tennessee-garage/dance-floor/models/Power Distribution.png

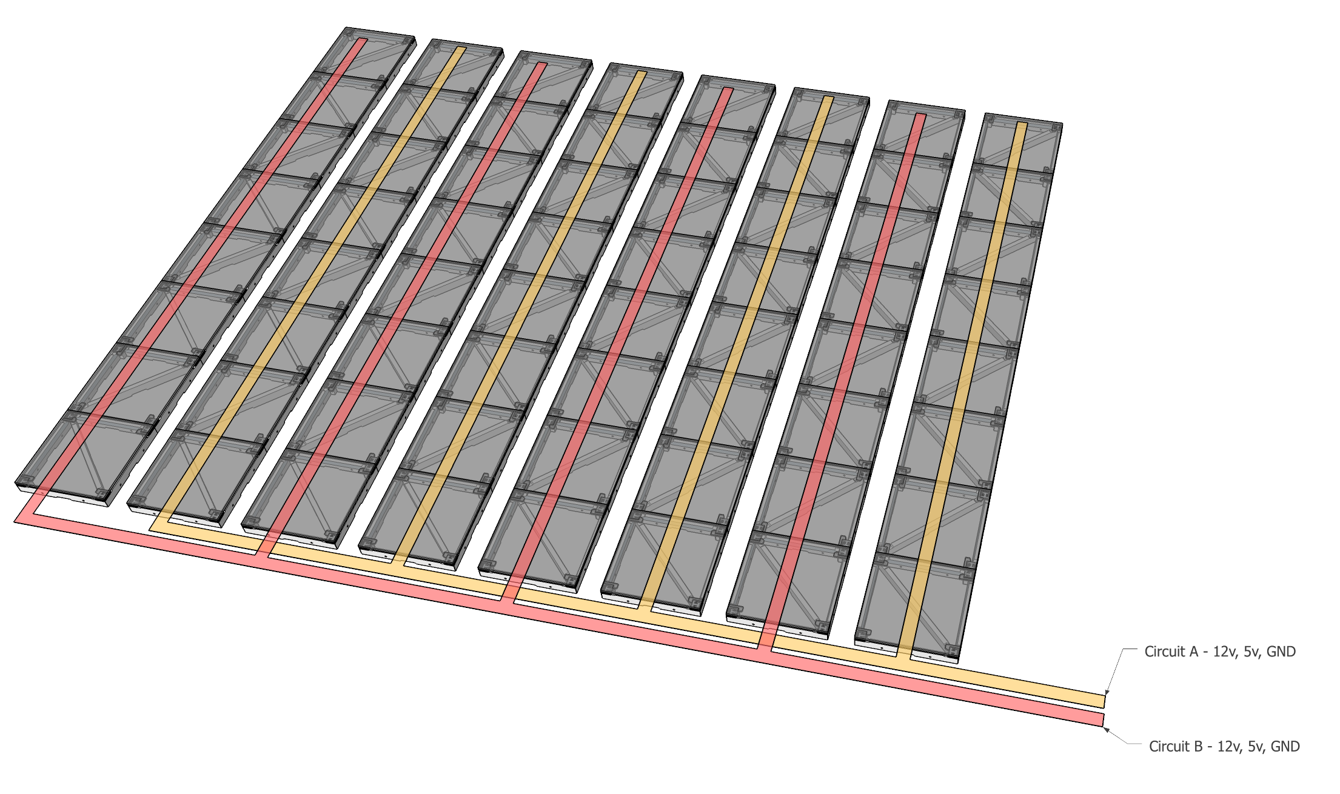
models/Power Distribution.png
