tennessee-garage/dance-floor/models/Floor Assembly - Detail.png

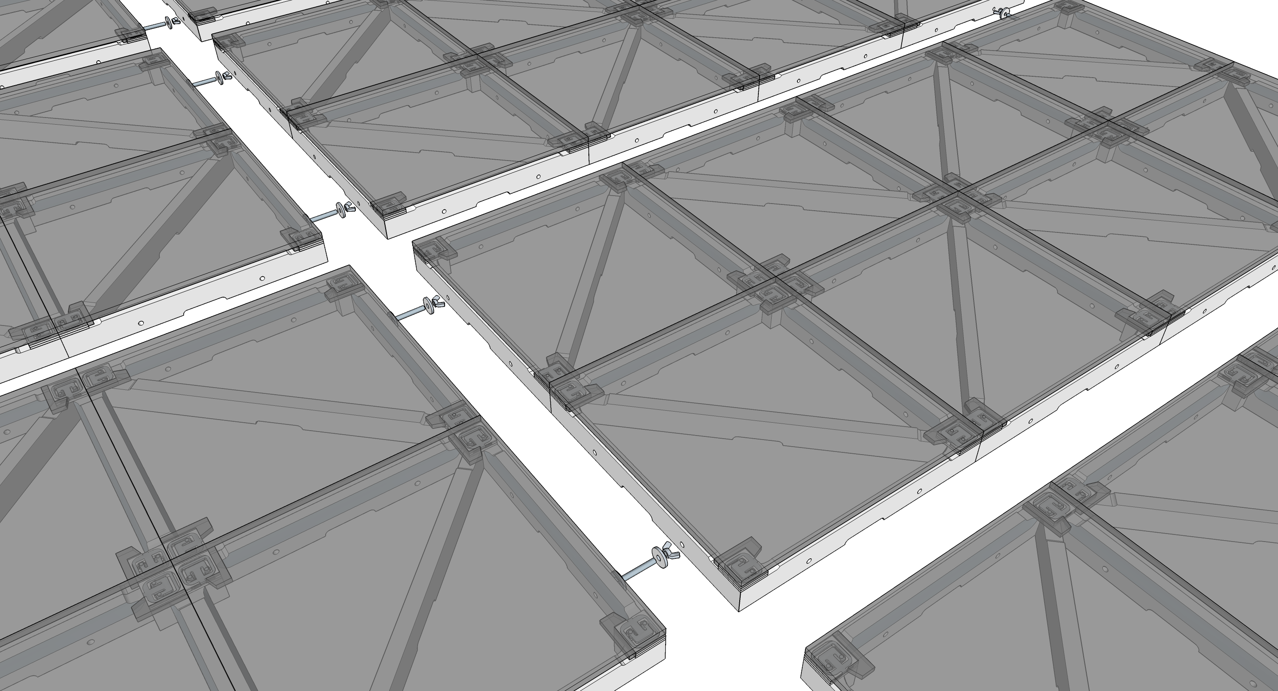
models/Floor Assembly - Detail.png
