tennessee-garage/dance-floor/models/Floor Assembly - Hardware.png

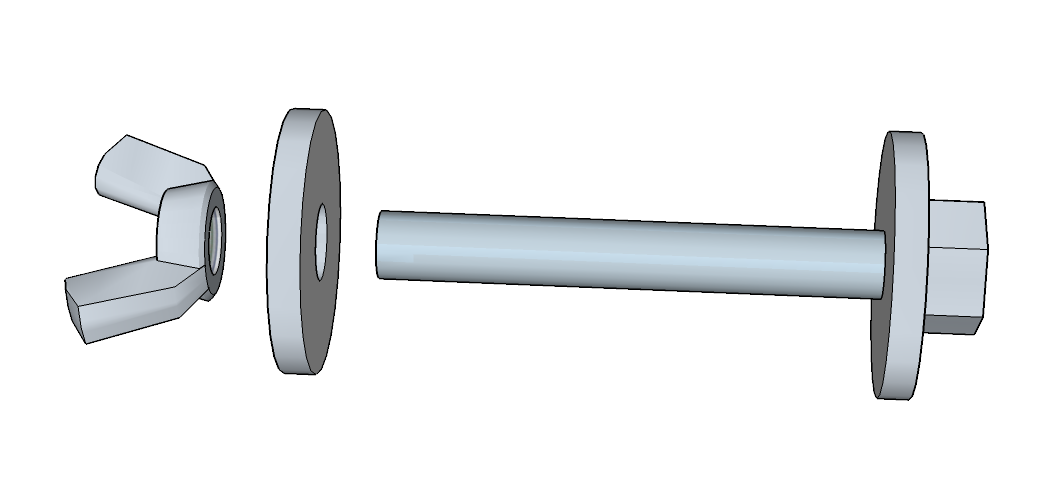
models/Floor Assembly - Hardware.png
