tennessee-garage/dance-floor/models/Floor Assembly - Overview.png

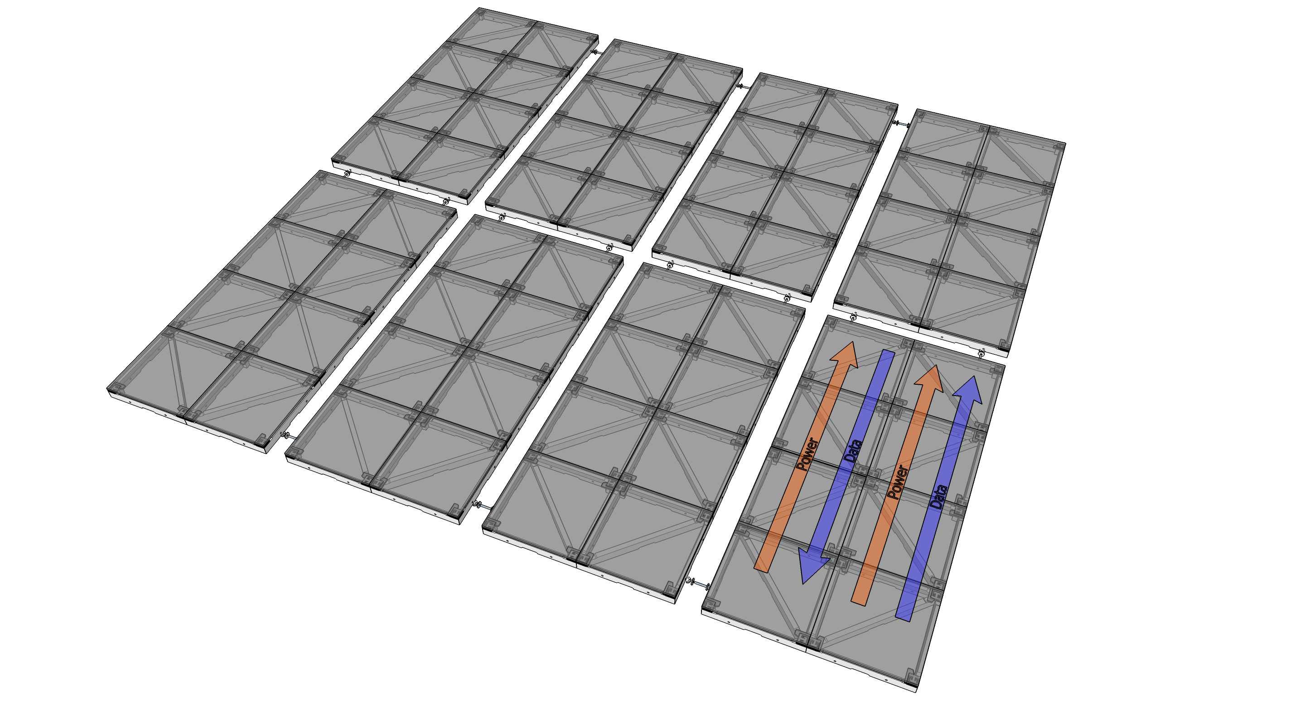
models/Floor Assembly - Overview.png
