tennessee-garage/dance-floor/floor/floor/processor/electricity.py

import logging
import math
import random

from floor.processor.base import Base
from floor.processor.utils import clocked

logger = logging.getLogger("electricity")


def dist(x1, y1, x2, y2):
    return math.sqrt((x1 - x2) ** 2 + (y1 - y2) ** 2)


class Electricity(Base):
    DECAY_RATE = 0.8
    DECAY_THRESHOLD = 0.001

    def __init__(self, **kwargs):
        super().__init__(**kwargs)

        self.arcs = {}

        # self.arc = Arc(1, 63)

        self.pixels = [[0, 0, 0] for _ in range(64)]

    @clocked(frames_per_second=24)
    def get_next_frame(self, context):
        weights = context.weights
        self.fade_frame()

        last_val = None
        new_arcs = {}
        for idx, w in enumerate(weights):
            if w > 0:
                if last_val is not None:
                    pair = f"{last_val}-{idx}"
                    logger.info(f"Pair: {pair}")
                    if pair in self.arcs:
                        new_arcs[pair] = self.arcs[pair]
                    else:
                        new_arcs[pair] = Arc(last_val, idx)

                last_val = idx

        self.arcs = new_arcs

        for arc in list(self.arcs.values()):
            self.apply_arc(arc)

        return self.pixels

    def apply_arc(self, arc):
        arc.advance()

        for idx, val in enumerate(arc.frame):
            if len(val) > 0:
                self.pixels[idx] = (
                    val  # [val * COLOR_MAXIMUM, val * COLOR_MAXIMUM, val * COLOR_MAXIMUM]
                )

    def fade_frame(self):
        for idx in range(64):
            if self.pixels[idx][0] > self.DECAY_THRESHOLD:
                self.pixels[idx][0] *= self.DECAY_RATE
                self.pixels[idx][1] *= self.DECAY_RATE
                self.pixels[idx][2] *= self.DECAY_RATE
            else:
                self.pixels[idx] = [0, 0, 0]


class Arc:
    LEAD_PATH = 1.0
    LEAD_ALTERNATE = 0.4

    def __init__(self, point1, point2):
        # Two points on the floor to arc between
        self.point1 = point1
        self.point2 = point2

        # The points translated to x & y
        self.p1x = point1 % 8
        self.p1y = int(point1 / 8)
        self.p2x = point2 % 8
        self.p2y = int(point2 / 8)

        logger.info(
            f"p1:{point1}, p2:{point2} == x1:{self.p1x}, y1:{self.p1y}, x2:{self.p2x}, y2:{self.p2y}"
        )

        # The position of the leading edge of the arc
        self.lead_x = self.p1x
        self.lead_y = self.p1y

        # The distance between the start and end point
        self.cur_distance = 0

        # Whether the arc has connected
        self.connected = False

        # Hold the arc pattern
        self.frame = [[0, 0, 0] for _ in range(64)]

    def advance(self):
        options = []
        self.set_cur_distance()

        # Upper left
        self.add_if_valid(options, self.lead_x - 1, self.lead_y - 1)

        # Upper center
        self.add_if_valid(options, self.lead_x, self.lead_y - 1)

        # Upper right
        self.add_if_valid(options, self.lead_x + 1, self.lead_y - 1)

        # Middle right
        self.add_if_valid(options, self.lead_x + 1, self.lead_y)

        # Lower right
        self.add_if_valid(options, self.lead_x + 1, self.lead_y + 1)

        # Lower middle
        self.add_if_valid(options, self.lead_x, self.lead_y + 1)

        # Lower left
        self.add_if_valid(options, self.lead_x - 1, self.lead_y + 1)

        # Middle left
        self.add_if_valid(options, self.lead_x - 1, self.lead_y)

        if len(options) == 0:
            return

        pick = random.randint(0, len(options) - 1)
        for idx, point in enumerate(options):
            if idx == pick:
                self.frame[point[0] + point[1] * 8] = [0, 0, 1000]
                self.lead_x = point[0]
                self.lead_y = point[1]
            else:
                self.frame[point[0] + point[1] * 8] = [500, 0, 0]

        if self.connected:
            # Start over again
            self.lead_x = self.p1x
            self.lead_y = self.p1y
            self.clear_frame()
            self.connected = False

    def set_cur_distance(self):
        self.cur_distance = self.dist_to_p2(self.lead_x, self.lead_y)

    def add_if_valid(self, options, x, y):
        d = self.dist_to_p2(x, y)
        if d != -1 and d < self.cur_distance:
            options.append((x, y))
        if d == 0:
            self.connected = True

    def dist_to_p2(self, x, y):
        if x < 0 or x > 7 or y < 0 or y > 7:
            return -1

        return dist(x, y, self.p2x, self.p2y)

    def clear_frame(self):
        self.frame = [[0, 0, 0] for _ in range(64)]
