tennessee-garage/dance-floor/floor/floor/processor/land_mines.py

import math
import random

import floor.util.color_utils as color_utils
from floor.processor.base import Base
from floor.processor.constants import COLOR_MAXIMUM
from floor.processor.utils import clocked

life_time = 4


class LandMines(Base):
    def __init__(self, **kwargs):
        super().__init__(**kwargs)
        self.pixels = []
        self.mines = []
        self.walkers = self.init_walkers()
        self.palette = color_utils.get_random_palette()
        self.palette_length = len(self.palette)
        for x in range(0, 8):
            for y in range(0, 8):
                self.pixels.append((0, 0, 0))

    @staticmethod
    def init_walkers():
        walkers = list()
        walkers.append({"x": 0, "y": 0})
        walkers.append({"x": 0, "y": 7})
        walkers.append({"x": 7, "y": 0})
        walkers.append({"x": 7, "y": 7})
        return walkers

    def get_walker(self):
        walker = self.walkers[random.randint(0, 2)]
        # take a random step
        walker["x"] += random.randint(-1, 1)
        if walker["x"] < 0:
            walker["x"] = 0
        if walker["x"] > 7:
            walker["x"] = 7
        walker["y"] += random.randint(-1, 1)
        if walker["y"] < 0:
            walker["y"] = 0
        if walker["y"] > 7:
            walker["y"] = 7
        return walker

    def build_mine(self, x, y):
        t = life_time

        idx = random.randint(0, self.palette_length - 1)
        return {"x": x, "y": y, "t": t, "color": self.palette[idx]}

    # For each mine in mines:
    # 1. If delta_time < life_time/2 Increment by: velocity * delta_time / radius
    # 2. If delta_time > life_time/2 Decrement by: velocity * delta_time / radius
    # 3. If delta_time > life_time, remove mine
    @clocked(frames_per_second=24)
    def get_next_frame(self, context):
        chance = random.random()
        if chance > 0.95:
            walker = self.get_walker()
            x = walker["x"]
            y = walker["y"]
            mine = self.build_mine(x, y)
            self.mines.append(mine)
            self.pixels[mine["y"] * 8 + mine["x"]] = mine["color"]

        time_delta = 0.1
        velocity = 0.0003 * COLOR_MAXIMUM
        live_mines = []
        for index in range(len(self.mines)):
            mine = self.mines[index]
            mine["t"] -= time_delta
            delta_time = life_time - mine["t"]
            color = mine["color"]
            toggle = 1

            # when the mine hits half a life_time, reverse the explosion
            if mine["t"] < life_time / 2:
                toggle = -1

            # if the mine has time left, compute explosion, store it in live_mines for next time
            if mine["t"] > 0.0:
                live_mines.append(mine)
                for y in range(0, 8):
                    for x in range(0, 8):
                        next_pixel = self.pixels[y * 8 + x]
                        radius = math.sqrt(
                            (x - mine["x"]) * (x - mine["x"]) + (y - mine["y"]) * (y - mine["y"])
                        )

                        # don't divide by zero :)
                        if radius > 0:
                            delta = toggle * velocity * delta_time / radius
                            next_red = next_pixel[0] + delta * color[0]
                            next_blue = next_pixel[1] + delta * color[1]
                            next_green = next_pixel[2] + delta * color[2]
                            # don't let values go negative
                            if next_blue < 0:
                                next_blue = 0
                            if next_red < 0:
                                next_red = 0
                            if next_green < 0:
                                next_green = 0
                            self.pixels[y * 8 + x] = (next_red, next_blue, next_green)

            # if the mine doesn't have time left, 0 it out and don't add it to live_mines
            else:
                self.pixels[mine["y"] * 8 + mine["x"]] = (0, 0, 0)

        self.mines = live_mines

        return self.pixels
