tennessee-garage/dance-floor/floor/floor/processor/animator.py

import importlib

from floor.processor.base import Base
from floor.processor.constants import COLOR_MAXIMUM
from floor.processor.utils import clocked
from floor.util.color_utils import scale_color


class Animator(Base):
    DEFAULT_ANIMATION = "gods_eye"

    def __init__(self, **kwargs):
        super().__init__(**kwargs)

        animation = kwargs.get("animation", self.DEFAULT_ANIMATION)

        module = importlib.import_module(f"floor.processor.animations.{animation}")
        self.animation = module.anim()
        self.floor_frame = 0
        self.animation_frame = 0
        self.fps_reduction = 2

    @clocked(frames_per_second=24)
    def get_next_frame(self, context):
        pixels = self.animation[self.animation_frame]

        if self.floor_frame % self.fps_reduction == 0:
            self.animation_frame = (self.animation_frame + 1) % len(self.animation)

        self.floor_frame = (self.floor_frame + 1) % 24

        pixels = [scale_color(p, COLOR_MAXIMUM / 255.0) for p in pixels]
        return pixels
