tennessee-garage/dance-floor/floor/floor/processor/ripple_pulse.py

import math

from floor.processor.ripple import Ripple
from floor.processor.utils import clocked


class RipplePulse(Ripple):
    # 0.75 is good for long pulses
    DECAY = 4
    OMEGA = 2 * math.pi

    # How much distance translates the time value sent to the decay method.
    # A number between 0.02 and 0.18 seems to look best.
    #  - Lower than 0.02 and the whole floor seems to flash at once
    #  - higher than 0.18 and there are too many striations and it looks noisy, not smooth
    DISTANCE_FACTOR = 0.03

    def __init__(self, **kwargs):
        super().__init__(**kwargs)

    @clocked(frames_per_beat=0.5)
    def reset_on_beat(self, context):
        self.t_start = context.clock
        self.hue += self.hue_rotation
        if self.hue > 1.0:
            self.hue -= 1.0
