tennessee-garage/dance-floor/floor/floor/processor/spiral_beat.py

from floor.processor.spiral import Spiral
from floor.processor.utils import clocked


class SpiralBeat(Spiral):
    @clocked(frames_per_beat=1)
    def get_next_frame(self, weights):
        super().get_next_frame(weights)
