tennessee-garage/dance-floor/poc_test/i2cCommands.h

//
// Created by Garth Webb on 3/18/17.
//

#ifndef DEMO2_I2CCOMMANDS_H
#define DEMO2_I2CCOMMANDS_H

void init_i2c(void);
void handle_i2c_command_last(void);
void handle_i2c_command_request_weight(void);
void handle_i2c_command_set_led(void);
void handle_i2c_command(void);
void handle_i2c(void);

#endif //DEMO2_I2CCOMMANDS_H
