tennessee-garage/dance-floor/floor/floor/processor/test.py

from floor.processor.base import Base
from floor.processor.constants import COLOR_MAXIMUM
from floor.processor.utils import clocked


class Test(Base):
    SLOW_CYCLE = 30
    FAST_CYCLE = 2

    def __init__(self, **kwargs):
        super().__init__(**kwargs)

        # helpful colors
        dark = (0, 0, 0)
        red = (COLOR_MAXIMUM, 0, 0)
        blue = (0, COLOR_MAXIMUM, 0)
        green = (0, 0, COLOR_MAXIMUM)

        # define cycles
        self.cycles = []
        # full-floor cycles
        self.cycles.append({"floor": self.init_floor(red), "duration": self.SLOW_CYCLE})
        self.cycles.append({"floor": self.init_floor(blue), "duration": self.SLOW_CYCLE})
        self.cycles.append({"floor": self.init_floor(green), "duration": self.SLOW_CYCLE})

        # cycles for individual squares
        for c in ["red", "blue", "green"]:
            for i in range(0, (self.FLOOR_WIDTH * self.FLOOR_HEIGHT)):
                floor = self.init_floor(dark)
                floor[i] = eval(c)
                self.cycles.append({"floor": floor, "duration": self.FAST_CYCLE})

        self.current_cycle = 0
        self.countdown = self.cycles[0]["duration"]

    def init_floor(self, initial_value):
        frame = []
        for x in range(0, (self.FLOOR_WIDTH * self.FLOOR_HEIGHT)):
            frame.append(initial_value)
        return frame

    @clocked(frames_per_second=24)
    def get_next_frame(self, context):
        self.countdown -= 1
        if self.countdown == 0:
            self.current_cycle += 1
            if self.current_cycle > len(self.cycles) - 1:
                self.current_cycle = 0
            self.countdown = self.cycles[self.current_cycle]["duration"]

        return self.cycles[self.current_cycle]["floor"]
