tennessee-garage/dance-floor/floor/floor/processor/test_step.py

from floor.processor.base import Base
from floor.processor.constants import COLOR_MAXIMUM
from floor.processor.utils import clocked
from floor.util import color_utils


def create(args=None):
    return StepTester()


class StepTester(Base):
    MAX_WEIGHT = 40

    def __init__(self):
        super().__init__()

    @clocked(frames_per_second=24)
    def get_next_frame(self, context):
        weights = context.weights
        pixels = []

        for idx in range(64):
            if idx < len(weights):
                w = weights[idx]
            else:
                w = 0

            val = color_utils.clamp(w, 0, 40)
            val = color_utils.remap(1.0 * val, 0, self.MAX_WEIGHT, 0, COLOR_MAXIMUM)
            pixels.append((val, val, 0))

        return pixels
