tennessee-garage/dance-floor/floor/floor/util/getch.py

def getch():
    import sys
    import termios
    import tty

    def _getch():
        fd = sys.stdin.fileno()
        old_settings = termios.tcgetattr(fd)
        try:
            tty.setraw(fd)
            ch = sys.stdin.read(1)
        finally:
            termios.tcsetattr(fd, termios.TCSADRAIN, old_settings)
        return ch

    return _getch()
